akkdong/MiniVario/doc/gps-alternate/0 Screen shot.jpg

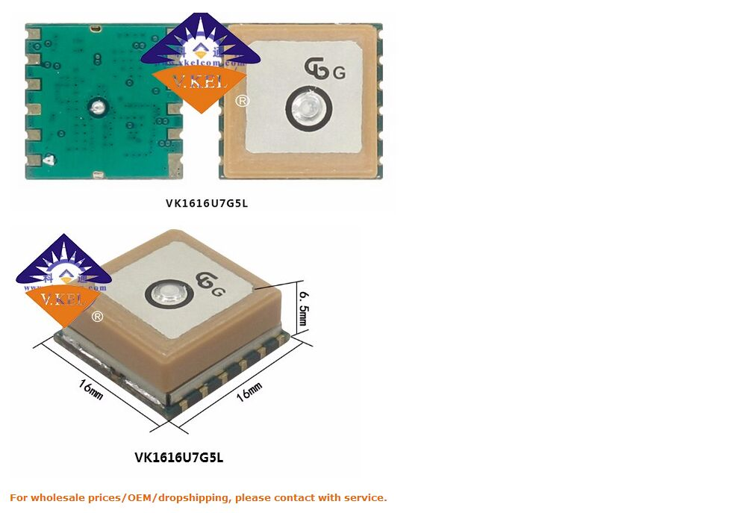
doc/gps-alternate/0 Screen shot.jpg
