akkdong/MiniVario/doc/gps-alternate/3 Recommended circuit.jpg

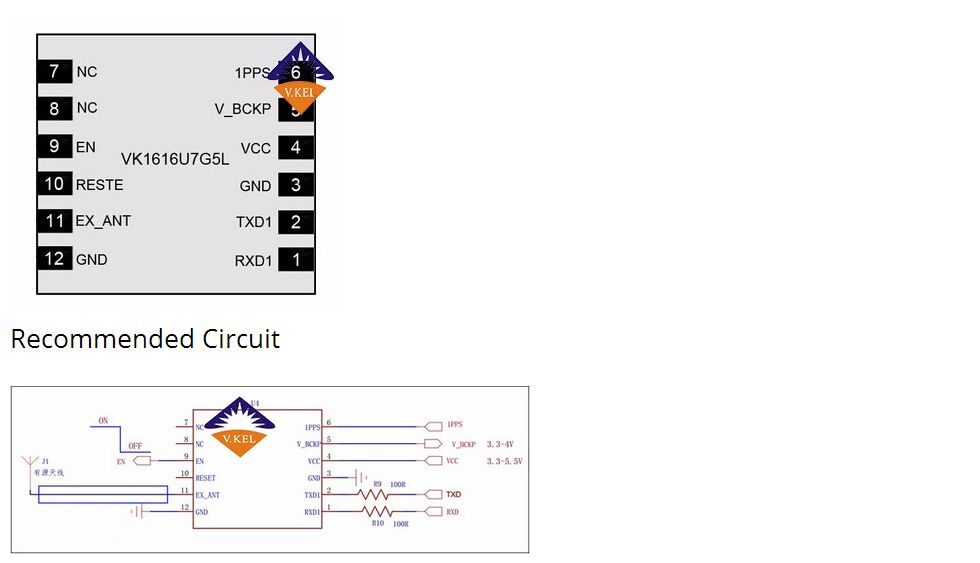
doc/gps-alternate/3 Recommended circuit.jpg
