akkdong/MiniVario/doc/gps-alternate/5 GPS and GLONASS Switching.jpg

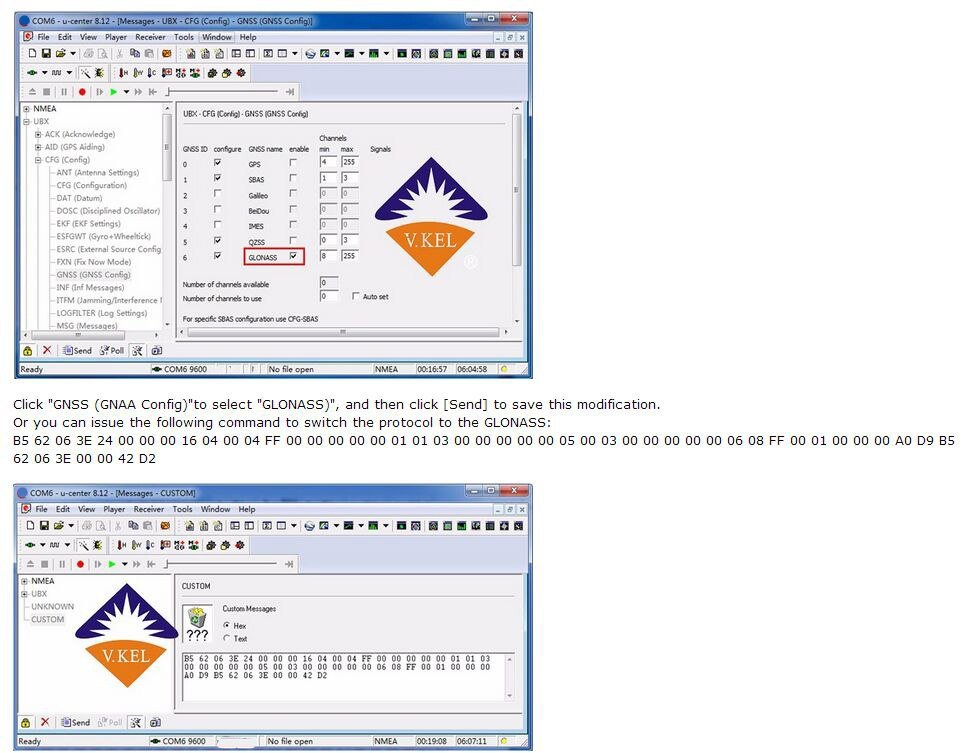
doc/gps-alternate/5 GPS and GLONASS Switching.jpg
