akkdong/MiniVario/doc/GY-91-1.jpg

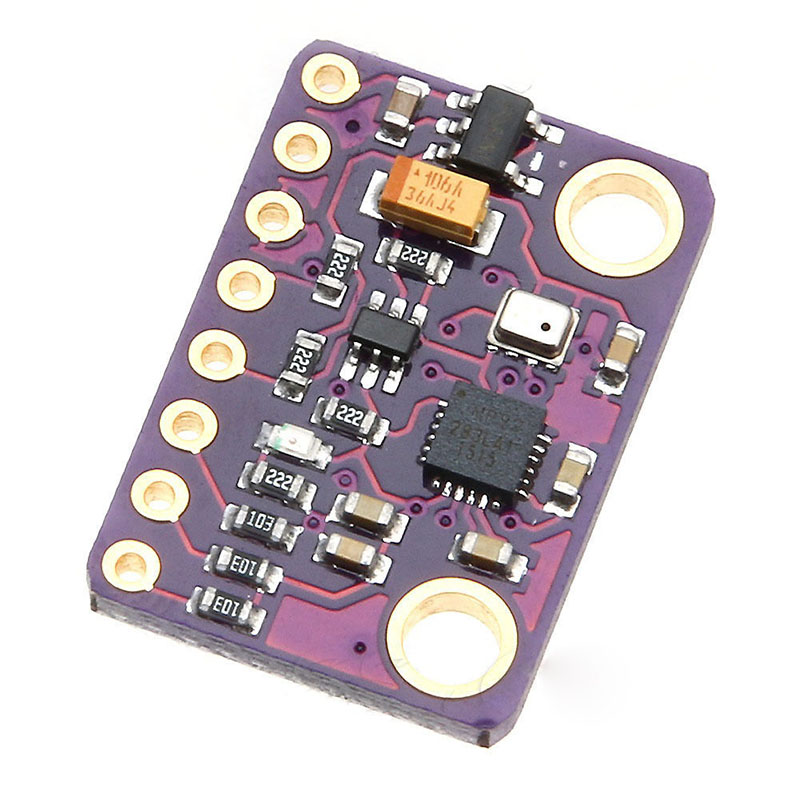
doc/GY-91-1.jpg
