akkdong/MiniVario/doc/ipex connector.jpg

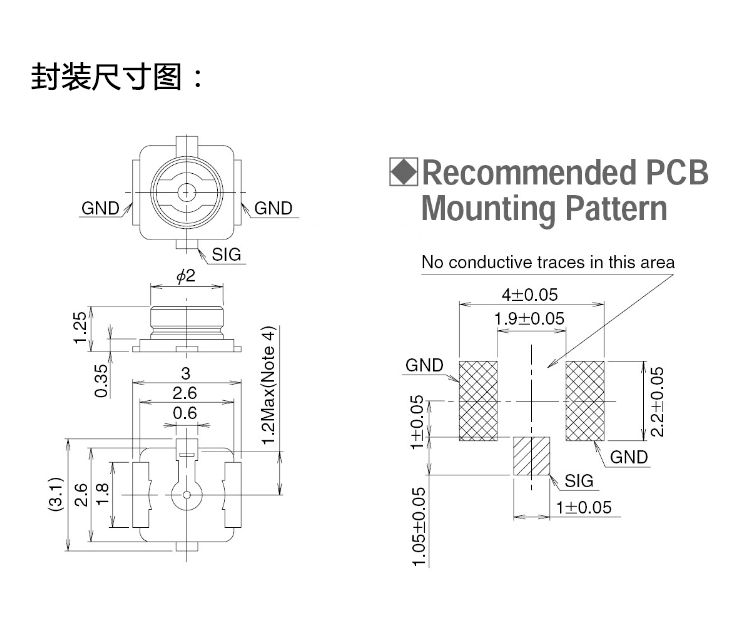
doc/ipex connector.jpg
