akkdong/MiniVario/doc/screenshot/screen01.bmp

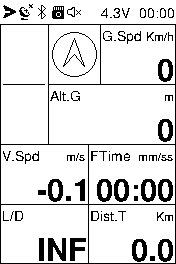
doc/screenshot/screen01.bmp
