akkdong/MiniVario/doc/screenshot/screen03.bmp

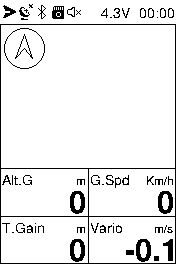
doc/screenshot/screen03.bmp
