akkdong/MiniVario/doc/screenshot/screen04.bmp

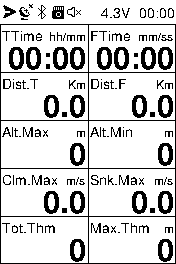
doc/screenshot/screen04.bmp
