akkdong/MiniVario/doc/screenshot/WebService.jpg

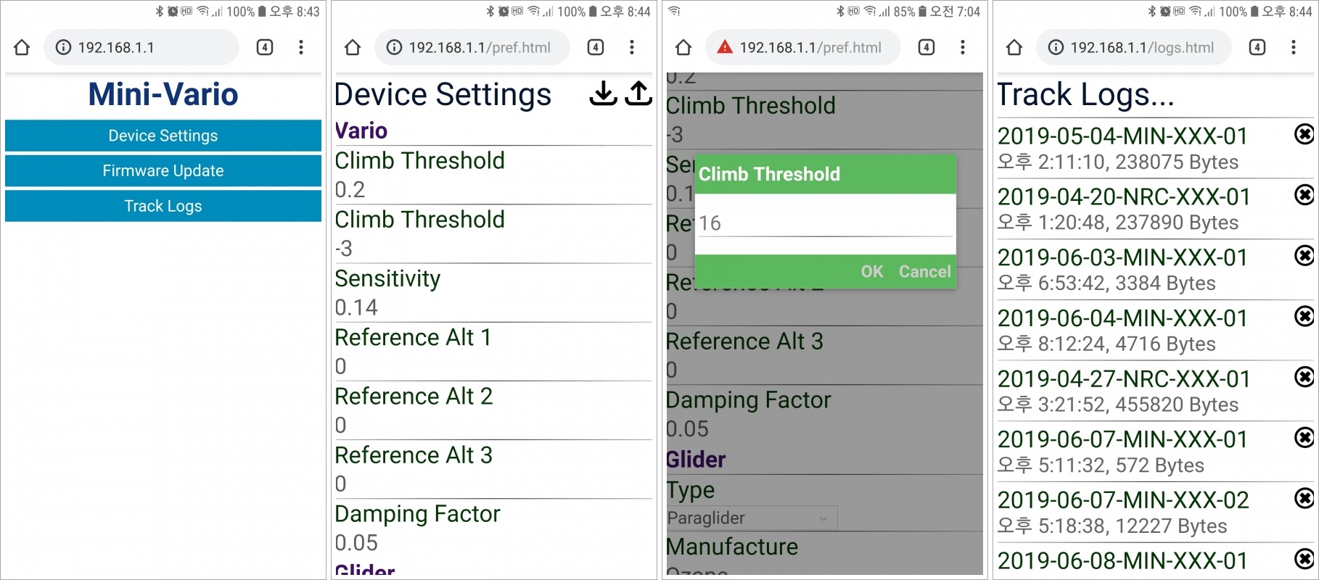
doc/screenshot/WebService.jpg
