akkdong/MiniVario/src-platformio/data/delete-button.png

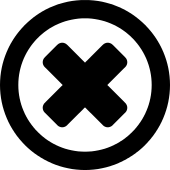
src-platformio/data/delete-button.png
