akkdong/MiniVario/src/test/WebService/data-working/download.png

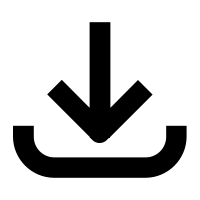
src/test/WebService/data-working/download.png
