akkdong/MiniVario/src/test/WebService/data-working/upload.png

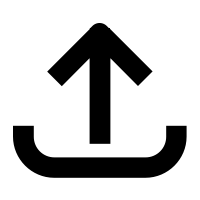
src/test/WebService/data-working/upload.png
