akkdong/MiniVario/doc/502774-0891.pdf

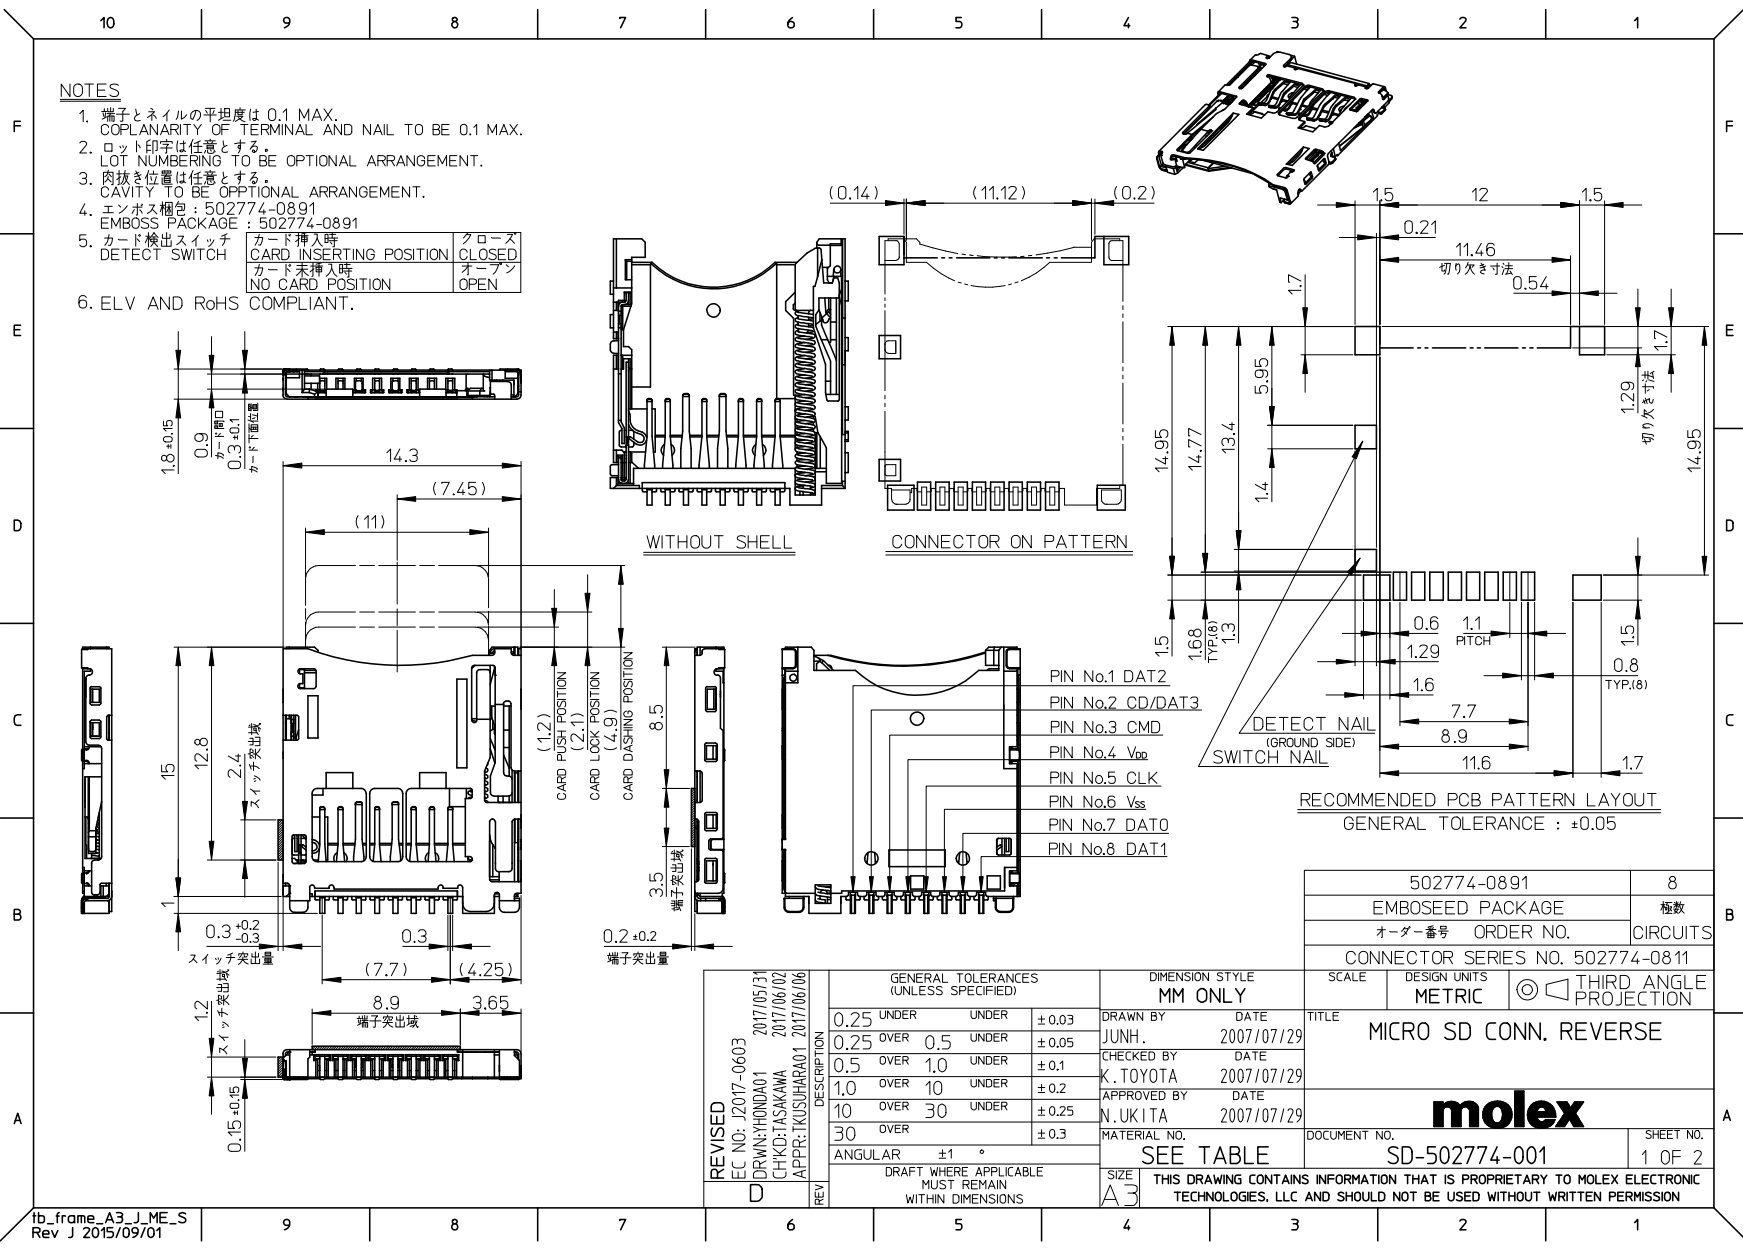
[picture p35: page 1]

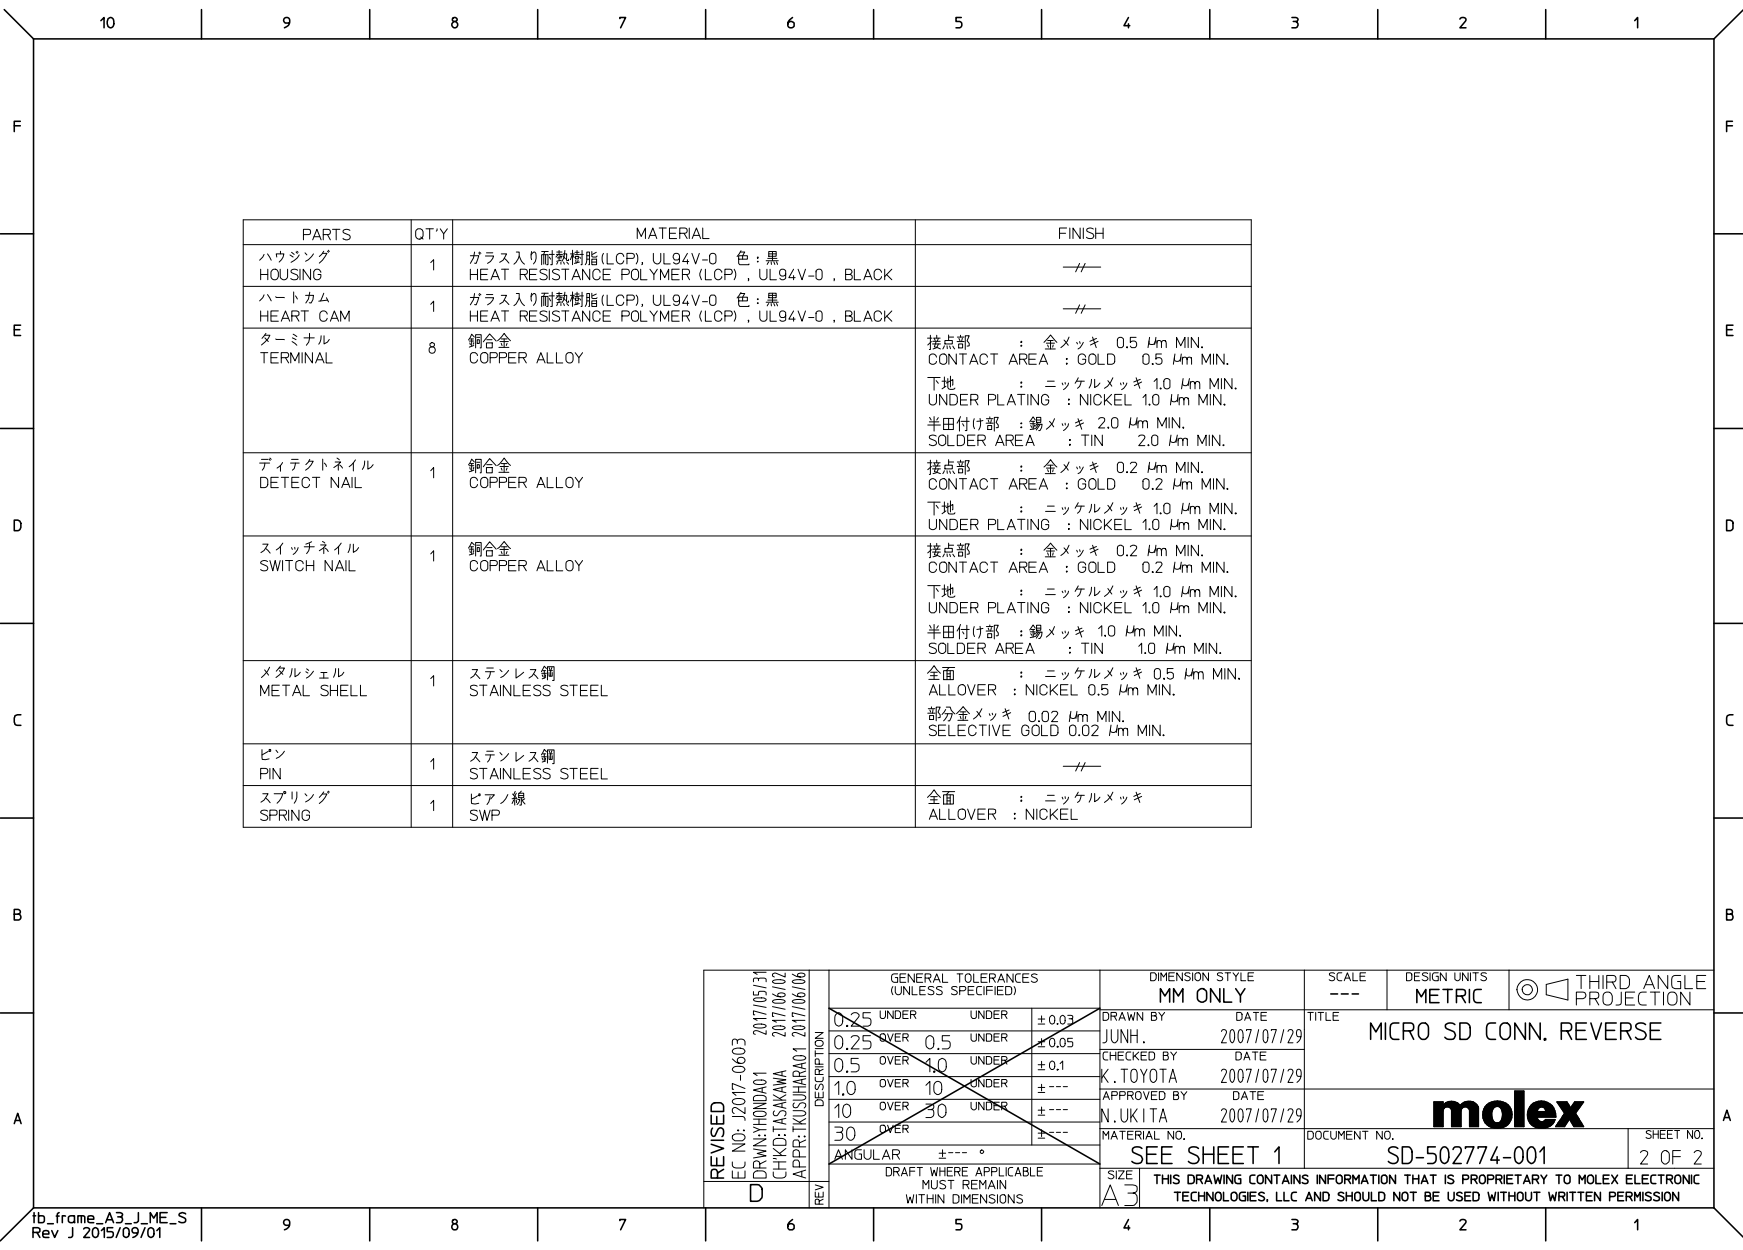
[picture p36: page 2]

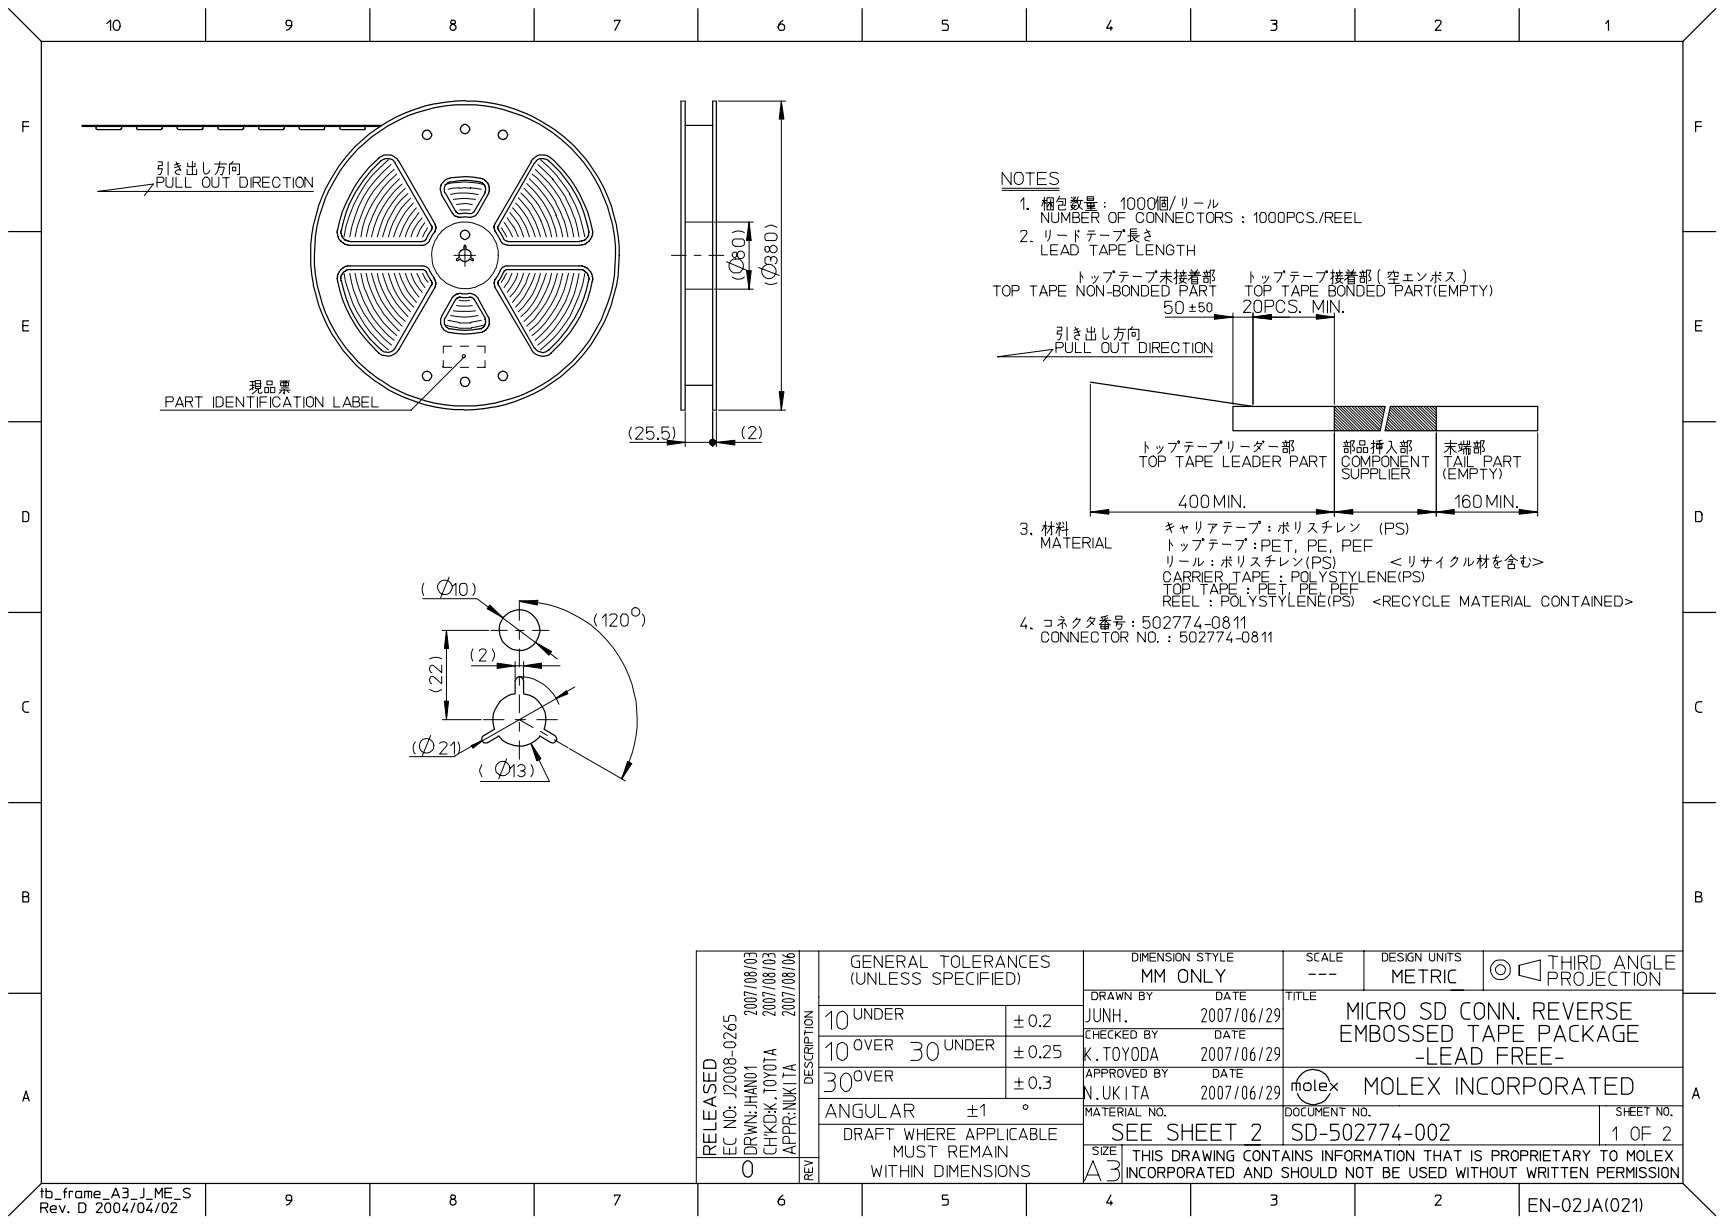
[picture p37: page 3]

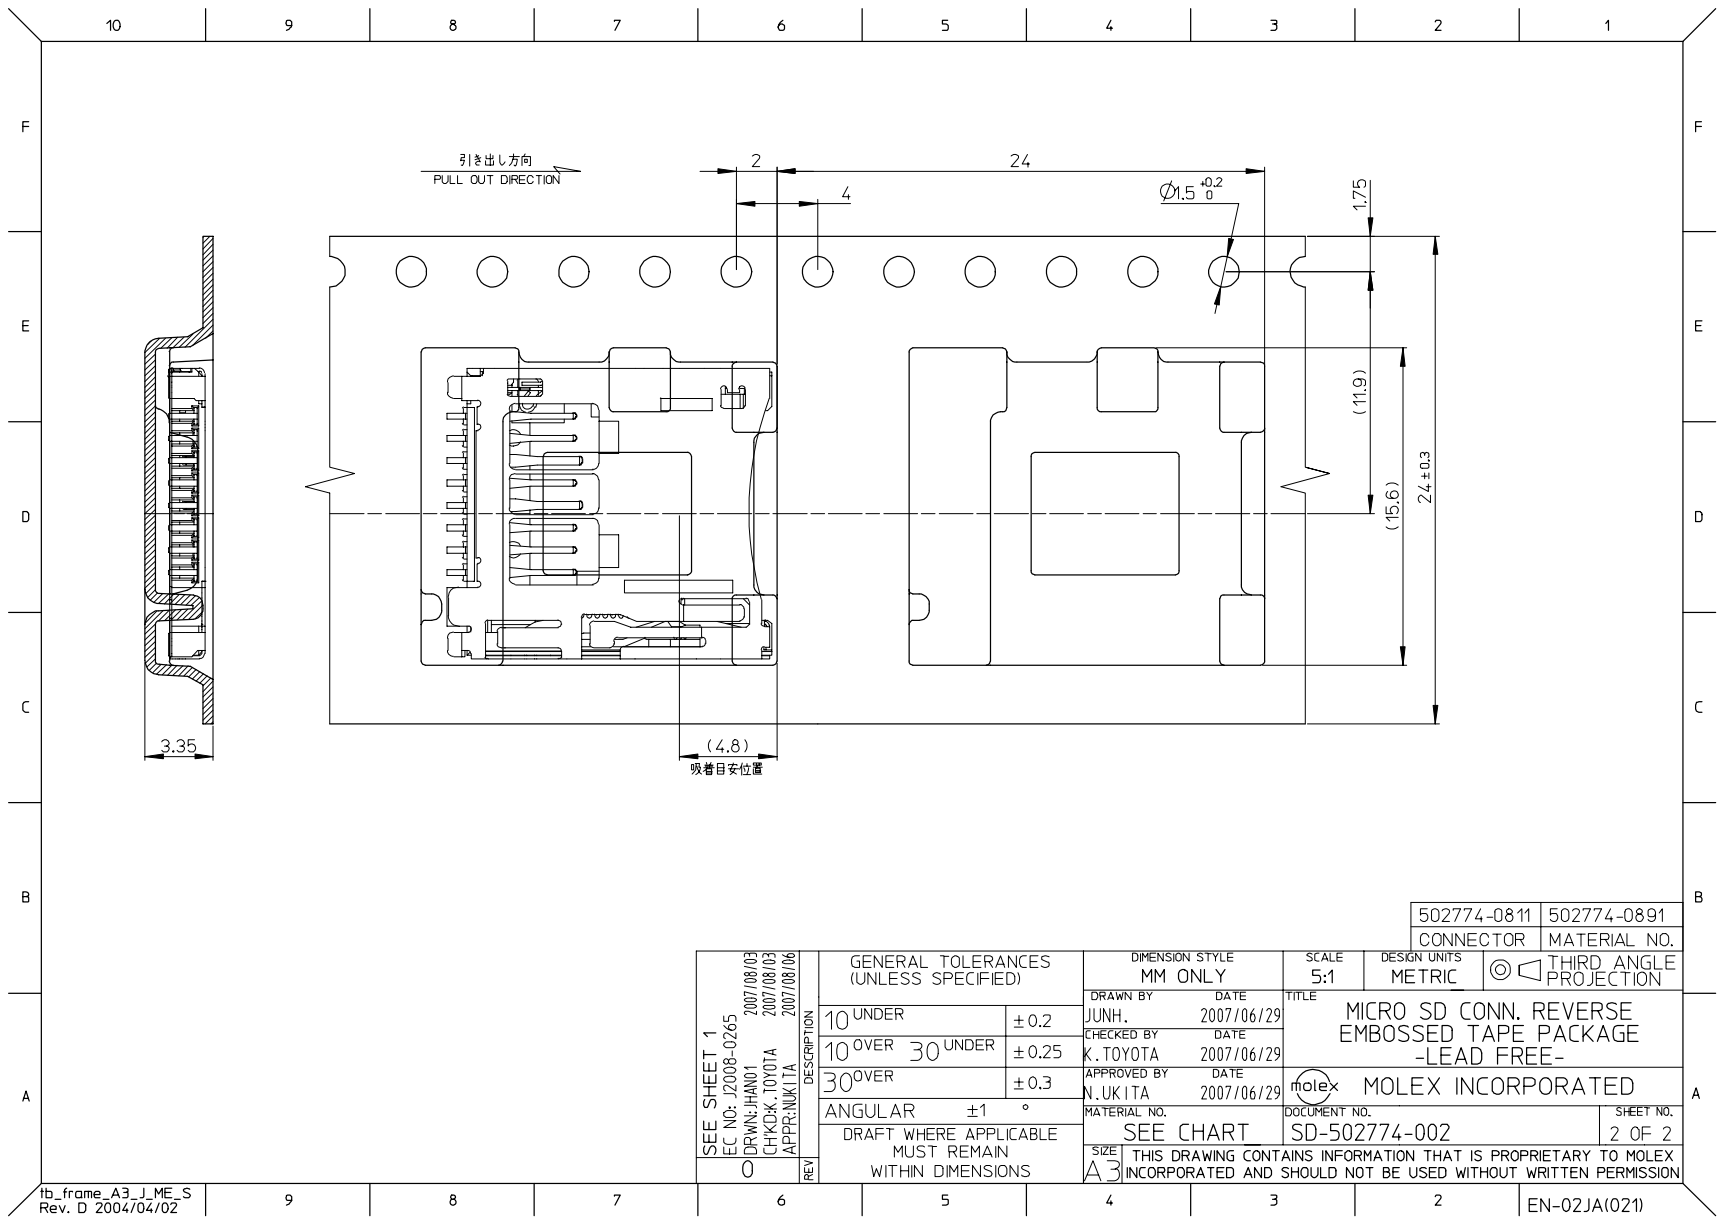
[picture p38: page 4]
