akkdong/MiniVario/doc/SML-LXR85GC-TR.pdf

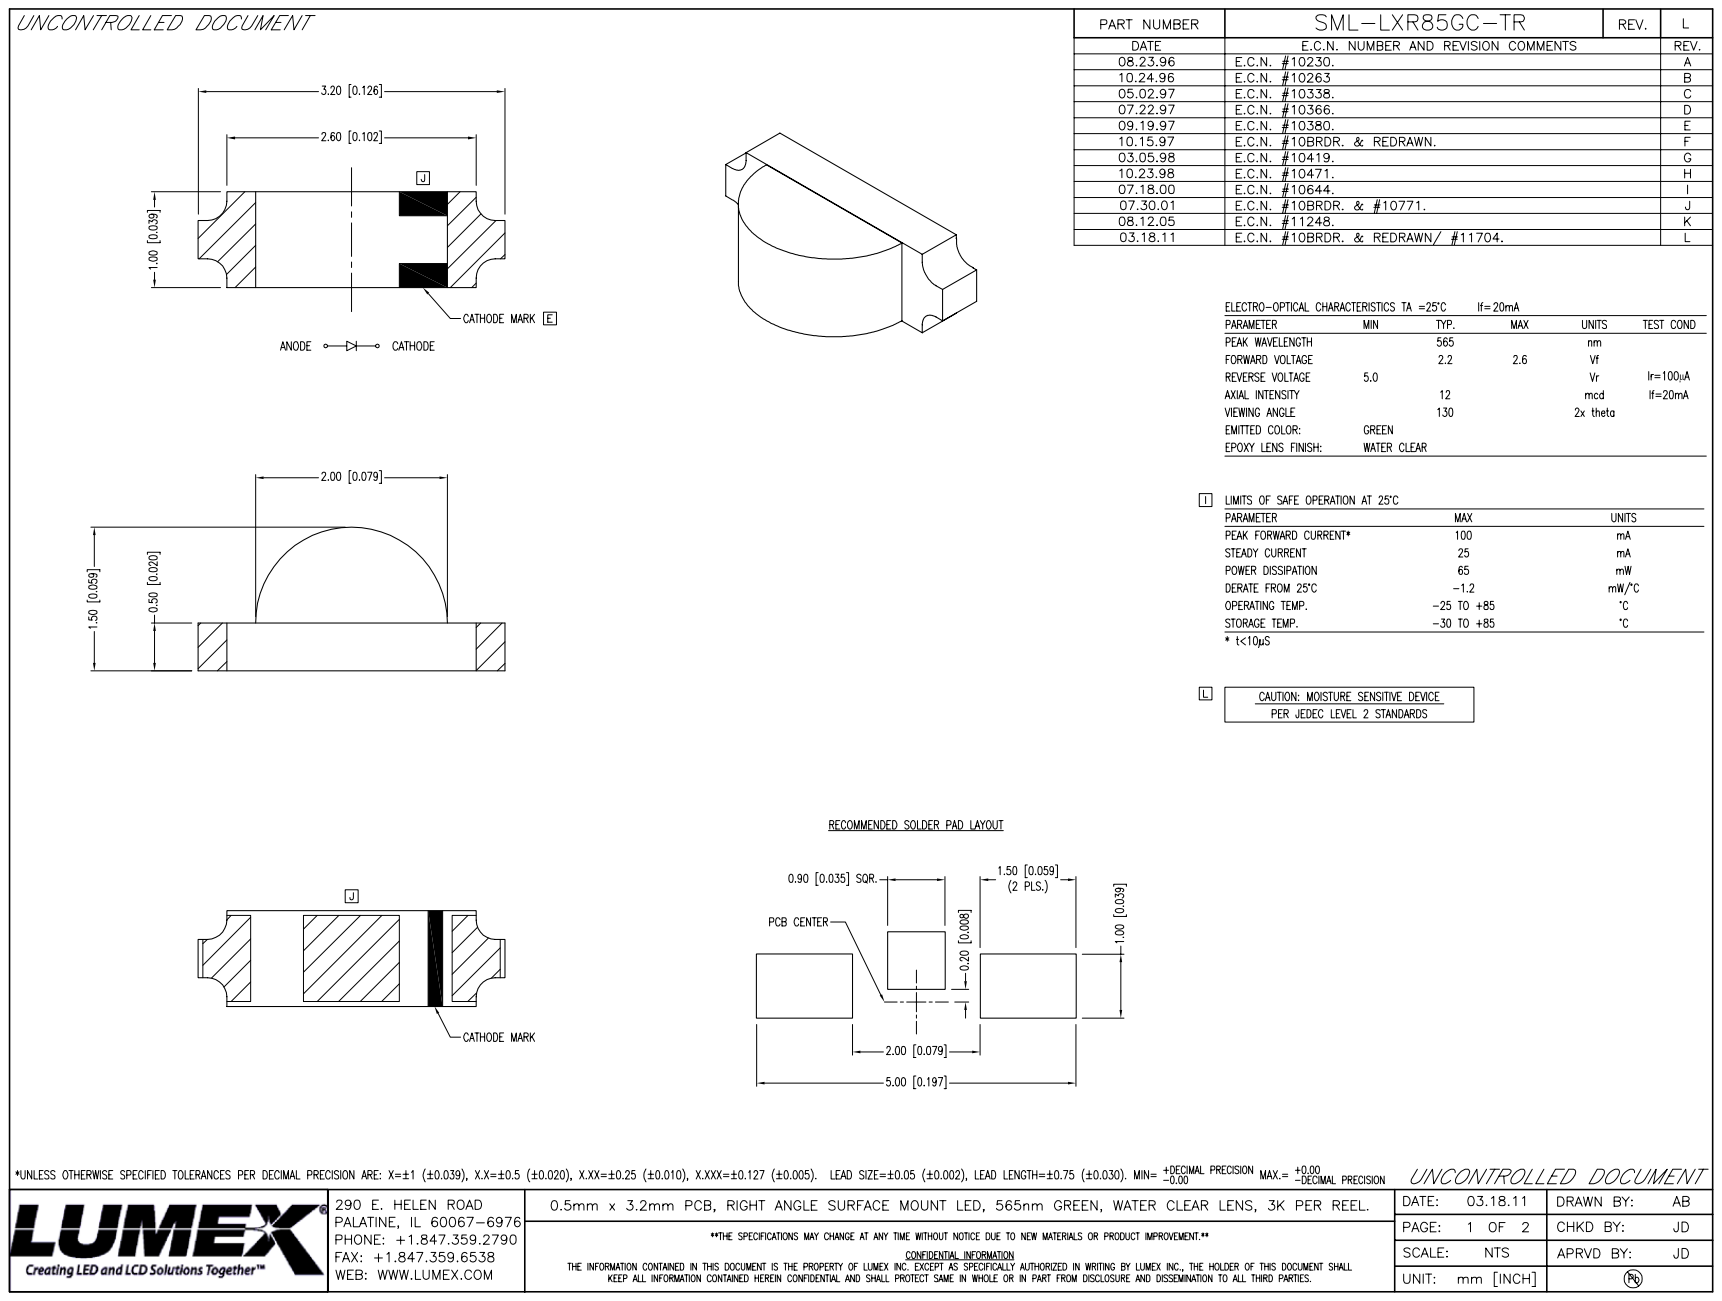
[picture p39: page 1]

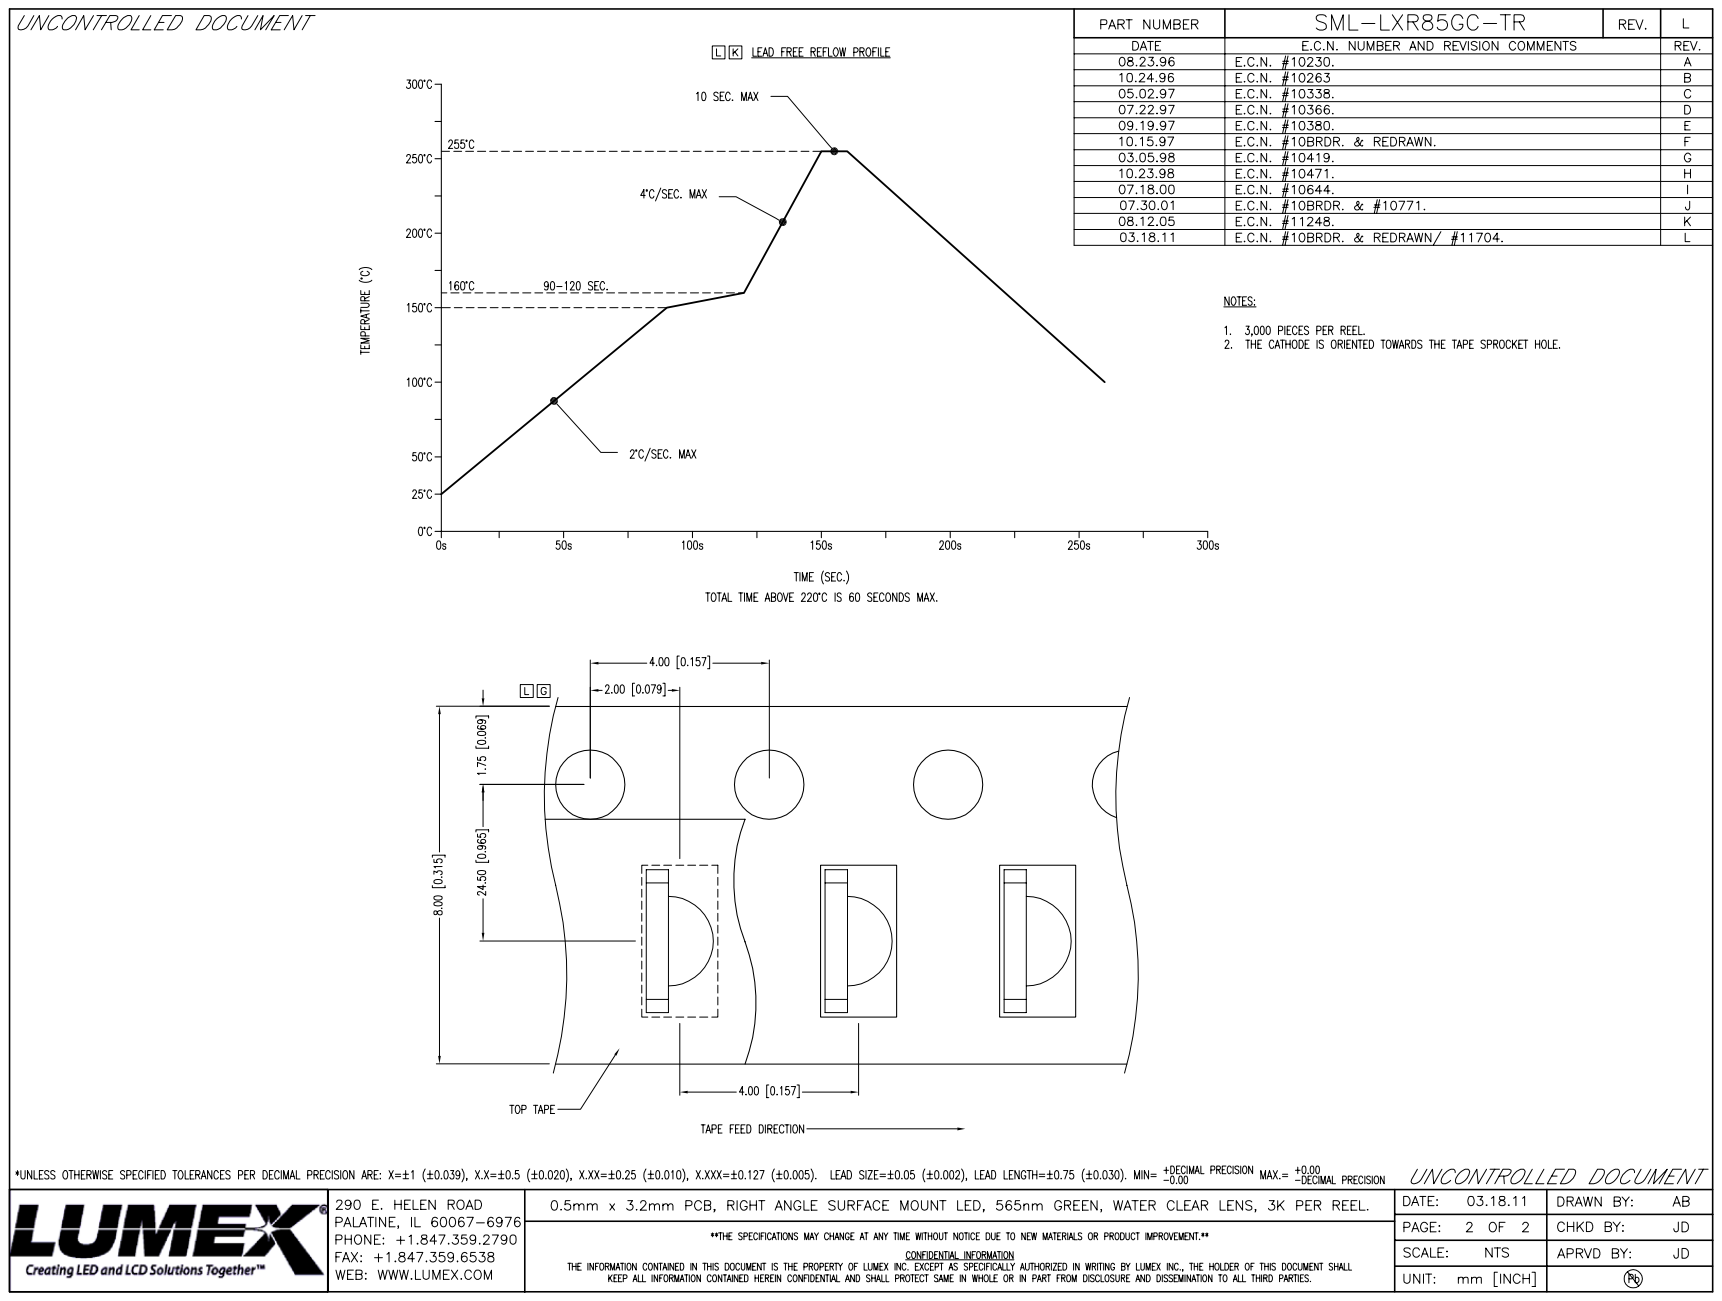
[picture p40: page 2]
