akkdong/MiniVario/src-platformio/src/WebService.h

// WebService.h
//

#ifndef __WEBSERVICE_H__
#define __WEBSERVICE_H__

#include <Arduino.h>
#include <WiFi.h>
#include <WebServer.h>
#include <ESPmDNS.h>
#include <SPIFFS.h>


///////////////////////////////////////////////////////////////////////////////////
// class WebServiceClass

class WebServiceClass : public WebServer
{
public:
    WebServiceClass();
    ~WebServiceClass();

public:
    void                start();
    void                stop();

    void                update();

protected:
    const char *        getContentType(String filename);

    bool                checkExist(fs::FS & fs, String path);
    bool                handleFileRead(fs::FS & fs, String path);

    static void         onUpdateRequest();
    static void         onRequestTrackLogs();
    static void         onDownloadTrackLog();
    static void         onDeleteTrackLog();
    static void         onRequest();

protected:
};


///////////////////////////////////////////////////////////////////////////////////
//

extern WebServiceClass  WebService;


#endif // __WEBSERVICE_H__
