akkdong/MiniVario/src-platformio/src/BluetoothCallback.h

// BluetoothCallback.h
//

#ifndef __BLUETOOTHCALLBACK_H__
#define __BLUETOOTHCALLBACK_H__

#include "BluetoothSerialEx.h"

/////////////////////////////////////////////////////////////////////////////////////////
//

void bluetoothSPPCallback(esp_spp_cb_event_t event, esp_spp_cb_param_t * param);


#endif // __BLUETOOTHCALLBACK_H__
