akkdong/MiniVario/src/test/Timer/Timer.ino

// Timer.ino
//

#include "HardwareTimer.h"

#if CONFIG_FREERTOS_UNICORE
#define ARDUINO_RUNNING_CORE 0
#else
#define ARDUINO_RUNNING_CORE 1
#endif

class TimerExample
{
public:
	TimerExample();
	
public:
	void								begin();
	
public:
	static void IRAM_ATTR 	TimerProc();
	static void 					TaskProc(void * param);
	
	static TimerExample *	mActive;
	
public:
	hw_timer_t *					mTimer;
	SemaphoreHandle_t		mSemaphore;
	portMUX_TYPE				mMux;
};

TimerExample * TimerExample::mActive = NULL;

TimerExample::TimerExample()
	: mTimer(NULL)
	, mSemaphore(xSemaphoreCreateBinary())
	, mMux(portMUX_INITIALIZER_UNLOCKED)
{
}

void TimerExample::begin()
{
	//
	digitalWrite(19, HIGH);
	pinMode(19, OUTPUT);
	
	//
	xTaskCreatePinnedToCore(
		TaskProc,  
		"TaskBaro",     // A name just for humans
		1024,   // This stack size can be checked & adjusted by reading the Stack Highwater
		this,  // Parameter
		2,    // Priority, with 3 (configMAX_PRIORITIES - 1) being the highest, and 0 being the lowest.
		NULL ,  
		ARDUINO_RUNNING_CORE);
	
	//
	mActive = this;
	mTimer = timerBegin(0, 80, true); // ESP32 Counter: 80 MHz, Prescaler: 80 --> 1MHz timer
	timerAttachInterrupt(mTimer, TimerProc, true);
	timerAlarmWrite(mTimer, 1000000 / 100, true); // 118Hz -> alarm every 8.4746 milliseconds  :  the measure period need to be greater than 8.22 ms
	timerAlarmEnable(mTimer);
}

void IRAM_ATTR TimerExample::TimerProc() 
{
	if (TimerExample::mActive != NULL)
	{
		BaseType_t xHigherPriorityTaskWoken = pdFALSE;
		xSemaphoreGiveFromISR(TimerExample::mActive->mSemaphore, &xHigherPriorityTaskWoken);
		if( xHigherPriorityTaskWoken == pdTRUE) 
			portYIELD_FROM_ISR(); // this wakes up task immediately instead of on next FreeRTOS tick
	}
}

void TimerExample::TaskProc(void * param) 
{
	//
	TimerExample * pThis = (TimerExample *)param;
	
	//
	int toggle = 1;
	digitalWrite(19, toggle);
	
	while (1)
	{
		//
		xSemaphoreTake(pThis->mSemaphore, portMAX_DELAY);
		
		//
		toggle = 1 -  toggle;
		digitalWrite(19, toggle);
	}
}

class MyTimer : public HardwareTimer
{
public:
	MyTimer() : HardwareTimer(TIMER_2) {		
		digitalWrite(19, LOW);
		pinMode(19, OUTPUT);
	}
	
	virtual void timerCallback() {
		static int toggle = 1;
		digitalWrite(19, toggle);
		toggle = 1 - toggle;
	}
};

TimerExample _TimerExample;
HardwareTimer hwTimer(TIMER_3);
MyTimer myTimer;


void _TestProc(void * param)
{
	static int toggle = 1;
	digitalWrite(23, toggle);
	toggle = 1 - toggle;
}

void setup()
{
	digitalWrite(23, HIGH);
	pinMode(23, OUTPUT);
	
//	_TimerExample.begin();

	#if 0
	myTimer.begin(80, true);
	myTimer.attachInterrupt(true);
	myTimer.alarmWrite(1000000 / 100, true); // 100Hz
	myTimer.alarmEnable();	
	#endif
	
	hwTimer.begin(80, true);
	hwTimer.attachInterrupt(_TestProc, true);
	hwTimer.alarmWrite(1000000 / 200, true); // 200Hz
	hwTimer.alarmEnable();	
}

void loop()
{
	// nop
}


#if 0 // OLD_EXAMPLE
volatile int interruptCounter;
int totalInterruptCounter;
volatile int on;
 
hw_timer_t * timer = NULL;
portMUX_TYPE timerMux = portMUX_INITIALIZER_UNLOCKED;
 
void IRAM_ATTR onTimer() {
  portENTER_CRITICAL_ISR(&timerMux);
  interruptCounter++;
  on = 1 - on;
  portEXIT_CRITICAL_ISR(&timerMux);
  
  digitalWrite(21, on ? HIGH : LOW);
}
 
void setup() {
 
  Serial.begin(115200);
 
  timer = timerBegin(0, 80, true); // ESP32 Counter: 80 MHz, Prescaler: 80 --> 1MHz timer
  timerAttachInterrupt(timer, onTimer, true);
  timerAlarmWrite(timer, 1000000 / 100, true); // 100Hz -> alarm every 10milliseconds
  timerAlarmEnable(timer);
  
  pinMode(21, OUTPUT);
  digitalWrite(21, HIGH);
}
 
void loop() {
 
  if (interruptCounter > 100) {
 
    portENTER_CRITICAL(&timerMux);
    interruptCounter = 0;
    portEXIT_CRITICAL(&timerMux);
 
    totalInterruptCounter++;
 
    Serial.print("An interrupt as occurred. Total number: ");
    Serial.println(totalInterruptCounter);
  }
}
#endif
