akkdong/MiniVario/src/apps/GpsSimulator/NmeaLoader.cpp

// NmeaLoader.cpp
//

#include "stdafx.h"
#include "NmeaLoader.h"





/////////////////////////////////////////////////////////////////////////////////////////////////
//

void TrimRight(char * str)
{
	int len = strlen(str);

	if (len > 0)
	{
		do
		{
			str[len] = NULL;
			--len;
		} while (len >= 0 && isspace(str[len]));
	}
}

int Tokenizer(char * tok[], int tokLen, char * str, const char * delimiter)
{
	char * ptr = str;
	int i = 0;

	// 
	tok[i] = ptr++;

	//
	while (*ptr && i < tokLen)
	{
		if (strchr(delimiter, *ptr) != NULL)
		{
			tok[++i] = ptr + 1;
			*ptr = NULL;
		}

		ptr++;
	}

	return i + 1;
}


time_t TimeString2Seconds(const char * str)
{
	int num = atoi(str);

	int h = num / 10000;
	num = num - h * 10000;
	int m = num / 100;
	num = num - m * 100;
	int s = num;

	return h * 3600 + m * 60 + s;
}

double NmeaCoordi2Decimal(const char * angle, const char * dir)
{
	// [D]DDMM.mmmmm
	double nmea = atof(angle);
	int dd = (int)(nmea / 100);
	double ss = nmea - (dd * 100.0);
	int sign = 1;

	if (strcmp(dir, "N") != 0 && strcmp(dir, "E"))
		sign = -1;

	return sign * (dd + ss / 60.0);
}

int compareNmeaTag(const char * name, const char * tag, bool ignoreTalker)
{
	int len1 = strlen(name);
	int len2 = strlen(tag);

	if (len1 != len2 || len1 != 5)
		return -1;

	const char* ptr1 = ignoreTalker ? &name[2] : &name[0];
	const char* ptr2 = ignoreTalker ? &tag[2] : &tag[0];

	return strcmp(ptr1, ptr2);	
}

int LoadNmea(LPCTSTR lpszFile, CPositionList & list)
{
	FILE * fp;

	USES_CONVERSION;
	if (fopen_s(&fp, T2A(lpszFile), "rt") == 0)
	{
		CString rmc, gga;
		time_t last = (time_t)-1;
		double lat = 0, lon = 0, alt = 0, speed = 0, track = 0;

		// reset list
		list.RemoveAll();

		while (!feof(fp))
		{
			//
			char line[256], temp[256];

			memset(line, 0, sizeof(line));
			fgets(line, sizeof(line), fp);
			if (line[0] != '$')
				continue;
			TrimRight(line);
			strcat_s(line, sizeof(line), "\r\n");

			memset(temp, 0, sizeof(temp));
			strcpy_s(temp, sizeof(temp), line);

			// test checksum
			if (0)
			{
				int checksum = 0;

				const char* ptr = &temp[1];
				while (*ptr)
				{
					checksum ^= ptr[0];

					if (ptr[0] == '*')
						break;

					ptr++;
				}
				TRACE("%s => %02X\n", line, checksum ^ '*');
			}

			//
#if 0
			char * tok[32], * context;
			int count = 0;

			for (int index = 0; index < sizeof(tok) / sizeof(tok[0]); index++)
			{
				if (index == 0)
					tok[index] = strtok_s(temp, ",", &context);
				else
					tok[index] = strtok_s(NULL, ",", &context);

				if (!tok[index])
					break;

				count = index + 1;
			}
#else
			char * tok[32];
			int count = Tokenizer(tok, sizeof(tok) / sizeof(tok[0]), temp, ",");
#endif

			if (count >= 10)
			{
				if (compareNmeaTag(&tok[0][1], "GPRMC", true) == 0 && strcmp(tok[2], "A") == 0) // fixed RMC only
				{
					time_t secs = TimeString2Seconds(tok[1]);

					if (!gga.IsEmpty() && last != secs)
						gga = _T("");

					/*
					if (gga.IsEmpty() || last == secs)
					{
						rmc = line;
						speed = atof(tok[7]) * 1.852;
						track = atof(tok[8]);
					}
					else // mismatch with time of rmc
					{
						gga = _T("");
						//rmc = _T("");
					}
					*/

					rmc = line;
					speed = atof(tok[7]) * 1.852;
					track = atof(tok[8]);
					last = secs;
				}
				else if (compareNmeaTag(&tok[0][1], "GPGGA", true) == 0 && strcmp(tok[6], "0") != 0)
				{
					time_t secs = TimeString2Seconds(tok[1]);

					if (!rmc.IsEmpty() && last != secs)
						rmc = _T("");

					/*
					if (rmc.IsEmpty() || last == secs)
					{
						gga = line;
						lat = NmeaCoordi2Decimal(tok[2], tok[3]);
						lon = NmeaCoordi2Decimal(tok[4], tok[5]);
						alt = atof(tok[9]);
					}
					else // mismatch with time of rmc
					{
						//gga = _T("");
						rmc = _T("");
					}
					*/

					gga = line;
					lat = NmeaCoordi2Decimal(tok[2], tok[3]);
					lon = NmeaCoordi2Decimal(tok[4], tok[5]);
					alt = atof(tok[9]);
					last = secs;
				}

				if (!gga.IsEmpty() && !rmc.IsEmpty())
				{
					//
					NmeaPosition * pos = new NmeaPosition;
					
					pos->rmc = rmc;
					pos->gga = gga;
					pos->_time = last;
					pos->latitude = lat;
					pos->longitude = lon;
					pos->altitude = alt;
					pos->speed = speed;
					pos->track = track;

					list.AddTail(pos);

					//
					gga = _T("");
					rmc = _T("");
				}
			}
		}

		fclose(fp);

		return list.GetCount();
	}

	return -1;
}
