akkdong/MiniVario/src/apps/GpsSimulator/resource.h

//{{NO_DEPENDENCIES}}
// Microsoft Visual C++ generated include file.
// Used by GpsSimulator.rc
//
#define IDD_GPSSIMULATOR_DIALOG         102
#define IDR_MAINFRAME                   128
#define IDI_REFRESH                     131
#define IDD_TRACK                       132
#define IDD_MONITOR                     136
#define IDC_LIST_NMEA                   1000
#define IDC_SERIAL_PORT                 1001
#define IDC_SERIAL_BAUDRATE             1002
#define IDC_REFRESH                     1003
#define IDC_CONNECT                     1004
#define IDC_LOAD                        1005
#define IDC_ACTION                      1006
#define IDC_PERIOD                      1007
#define IDC_FRAME                       1007
#define IDC_AUTO_SCROLL                 1008
#define IDC_MESSAGE                     1009
#define IDC_CONTENT                     1010

// Next default values for new objects
// 
#ifdef APSTUDIO_INVOKED
#ifndef APSTUDIO_READONLY_SYMBOLS
#define _APS_NEXT_RESOURCE_VALUE        138
#define _APS_NEXT_COMMAND_VALUE         32771
#define _APS_NEXT_CONTROL_VALUE         1011
#define _APS_NEXT_SYMED_VALUE           105
#endif
#endif
