akkdong/MiniVario/src/apps/GpsSimulator/stdafx.cpp

// stdafx.cpp : source file that includes just the standard includes
// GpsSimulator.pch will be the pre-compiled header
// stdafx.obj will contain the pre-compiled type information

#include "stdafx.h"
