akkdong/MiniVario/src/test/Temperature/Task.h

// Task.h
//

#ifndef __TASK_H__
#define __TASK_H__

///////////////////////////////////////////////////////////////////////////////////////////////////////////////
// class Task

class Task
{
protected:
	Task():
	
protected:
	static void 					TaskProc(void * param);

};


#endif // __TASK_H__
